furkanbakkal/STM32-Stepper-Motor-Driver/render/1.png

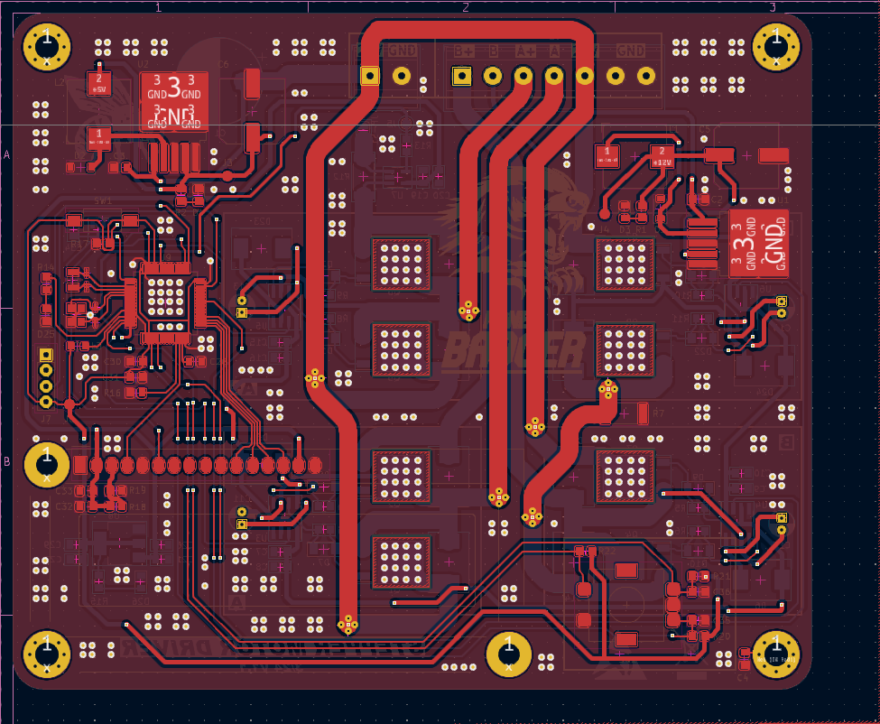
render/1.png
