furkanbakkal/STM32-Stepper-Motor-Driver/render/2.png

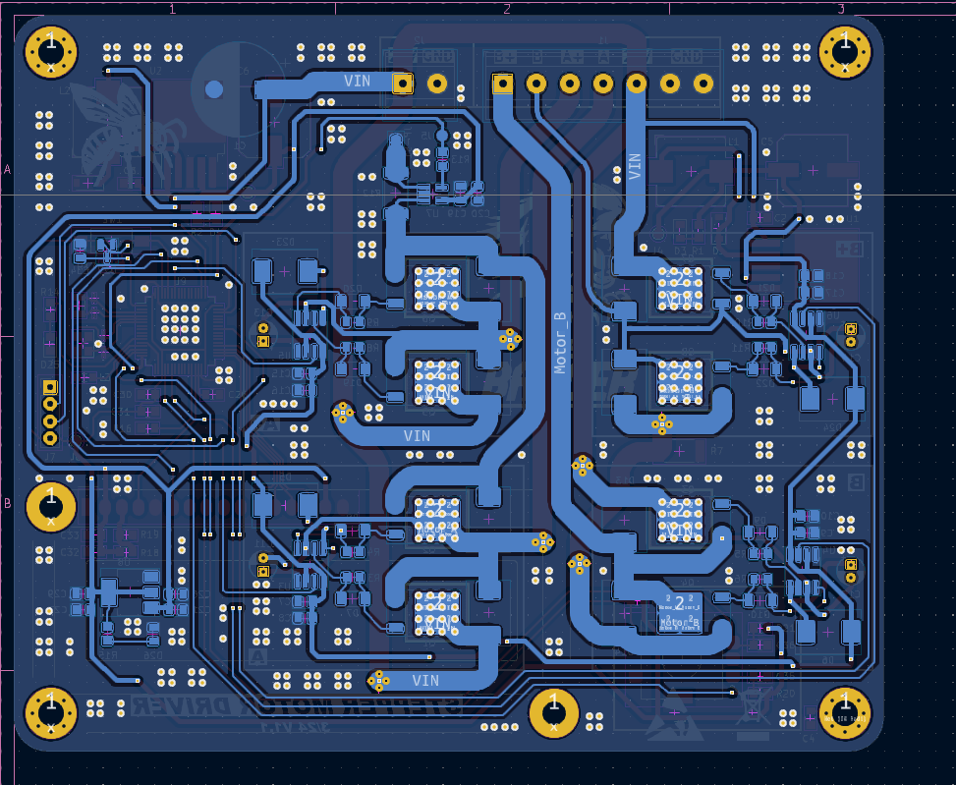
render/2.png
